nayaramadan/The-Incredible-Rockasis/images/8.jpg

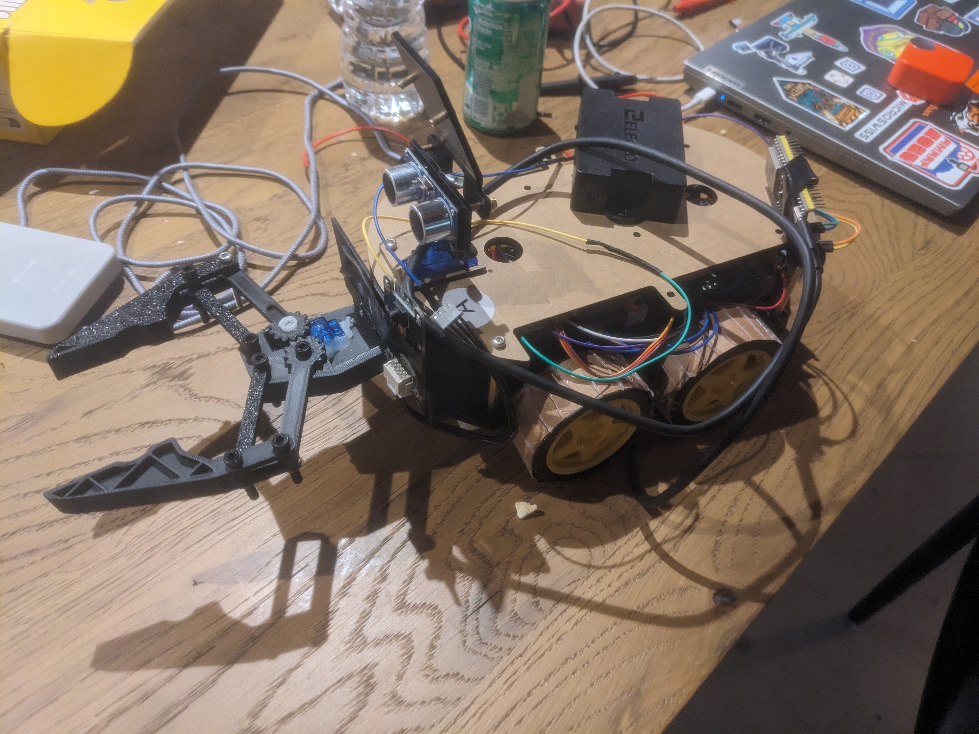
images/8.jpg
